microferret/Set-Phasers-to-Killin-/Customshift_Phaser/Pasted image 20251223214937.png

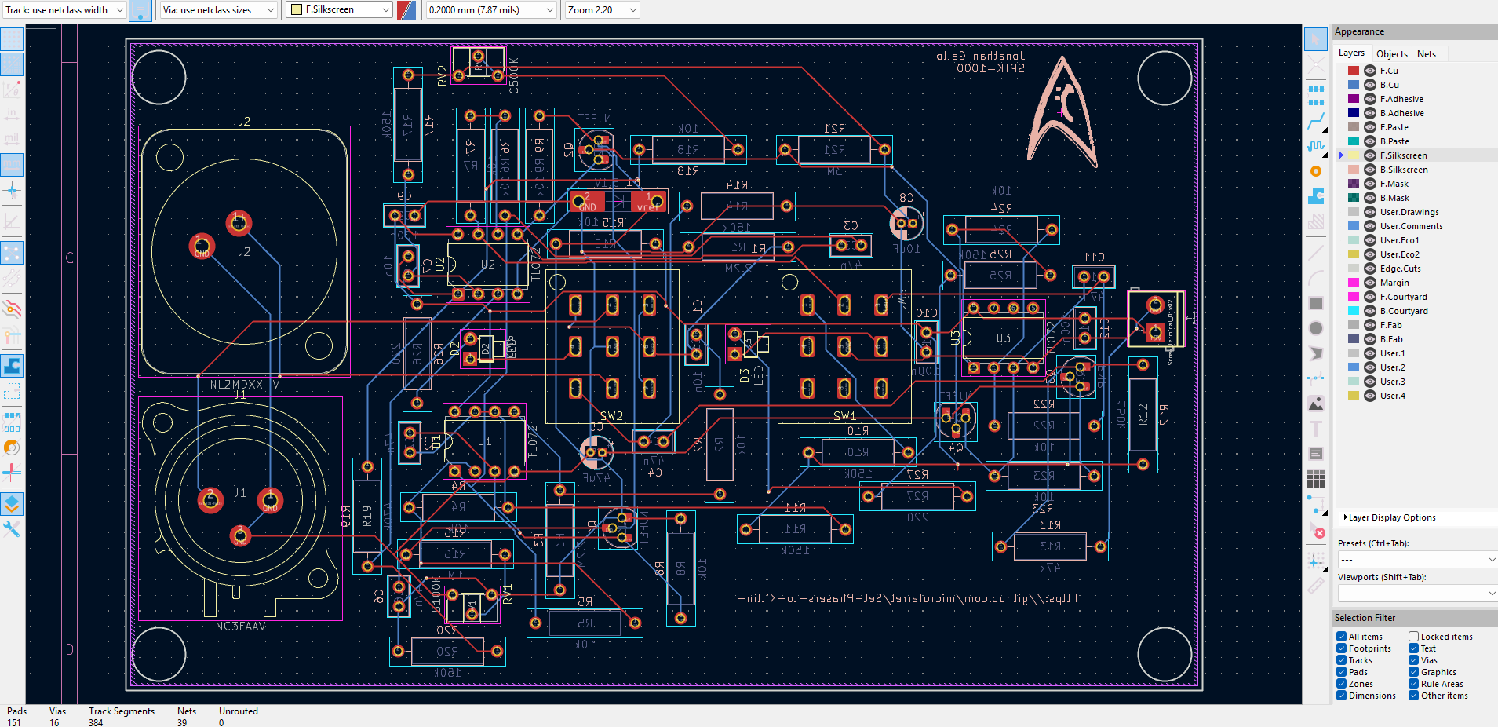
Customshift_Phaser/Pasted image 20251223214937.png
