microferret/Set-Phasers-to-Killin-/Customshift_Phaser/Pasted image 20251226221127.png

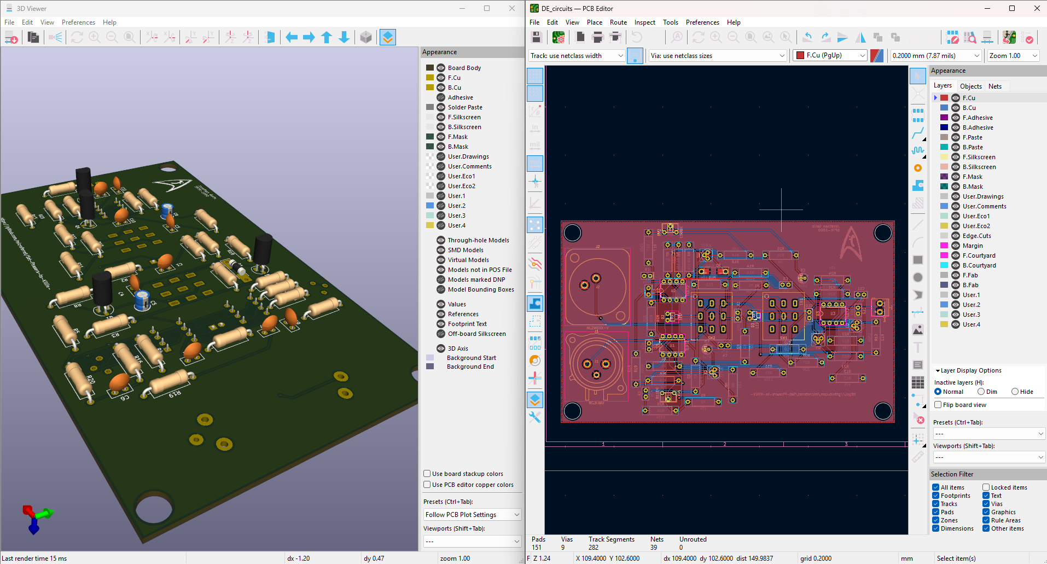
Customshift_Phaser/Pasted image 20251226221127.png
