microferret/Set-Phasers-to-Killin-/Customshift_Phaser/Screenshot 2026-02-16 173127.png

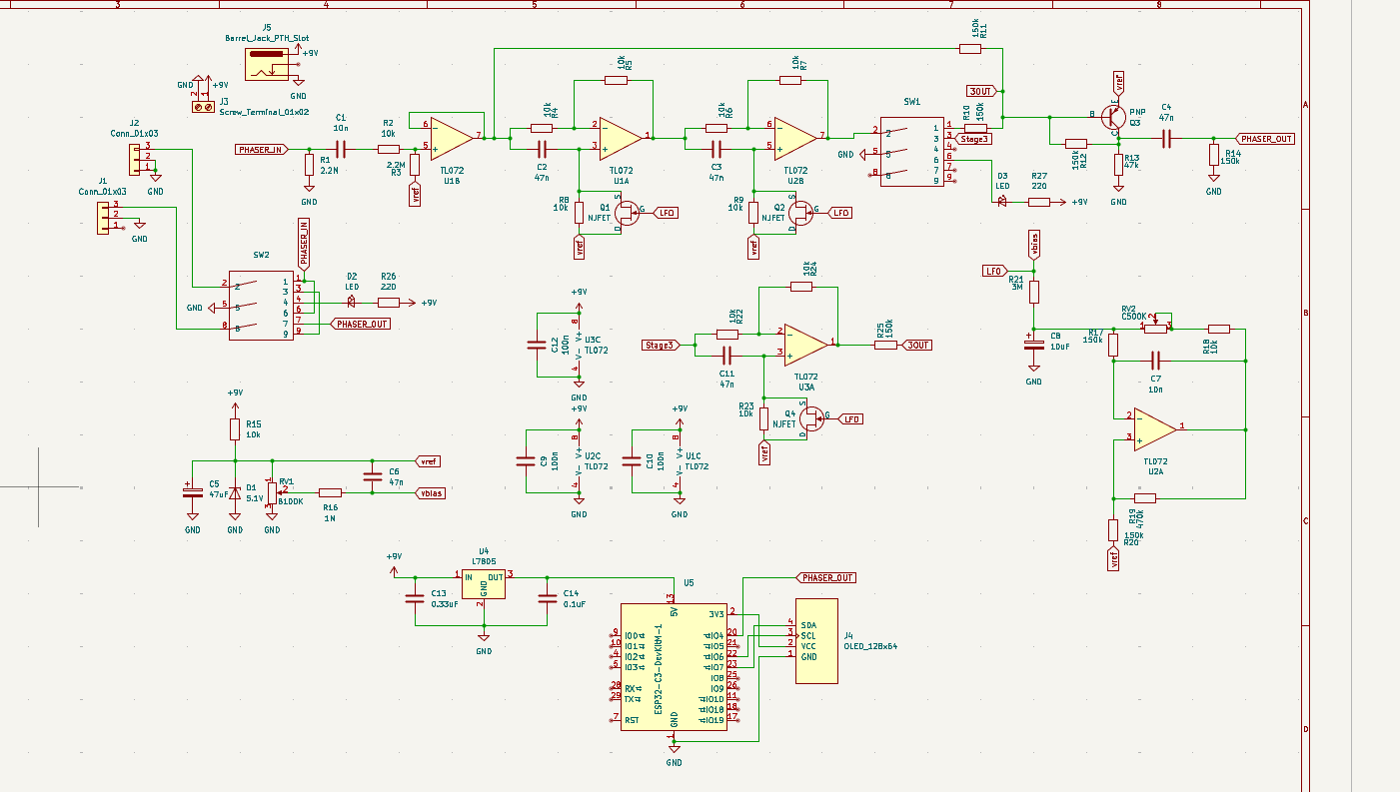
Customshift_Phaser/Screenshot 2026-02-16 173127.png
